timkoehne/myStreamdeck/keycap images/deafen.png

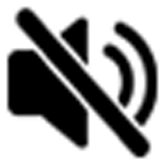
keycap images/deafen.png
