timkoehne/myStreamdeck/keycap images/light.png

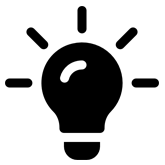
keycap images/light.png
