timkoehne/myStreamdeck/keycap images/play_pause.png

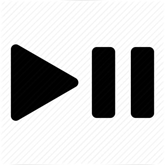
keycap images/play_pause.png
